Reverier-Xu/KeysDock/arts/nijika.png

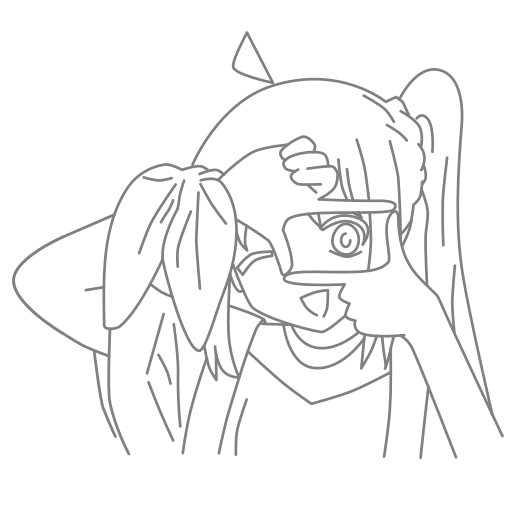
arts/nijika.png
