Reverier-Xu/KeysDock/suitekits/KeysDock.FCStd

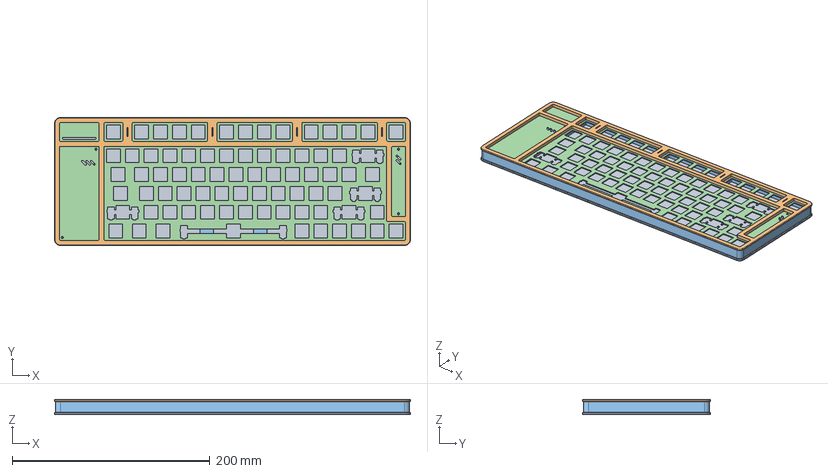
[picture p18: CAD file, 2026-06-06]
suitekits/KeysDock.FCStd
359.8 x 129.3 x 15.0 mm
Base
Cover
Center
Plate
