Reverier-Xu/KeysDock/hardware/models/TPD4E05U06DQAR.step

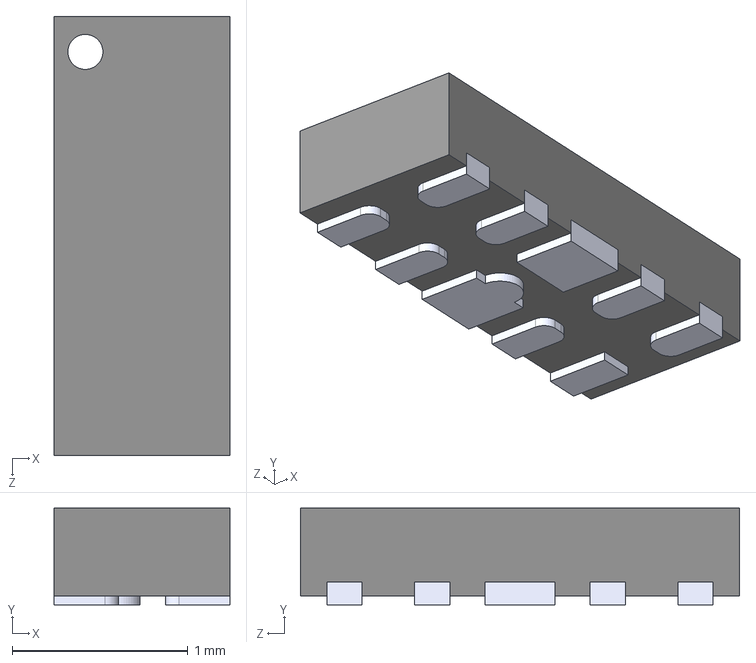
[picture p19: CAD file, 2026-03-23]
hardware/models/TPD4E05U06DQAR.step
1.00 x 0.55 x 2.50 mm
