Reverier-Xu/KeysDock/hardware/models/LED-SMD_XL-3512RGBW.step

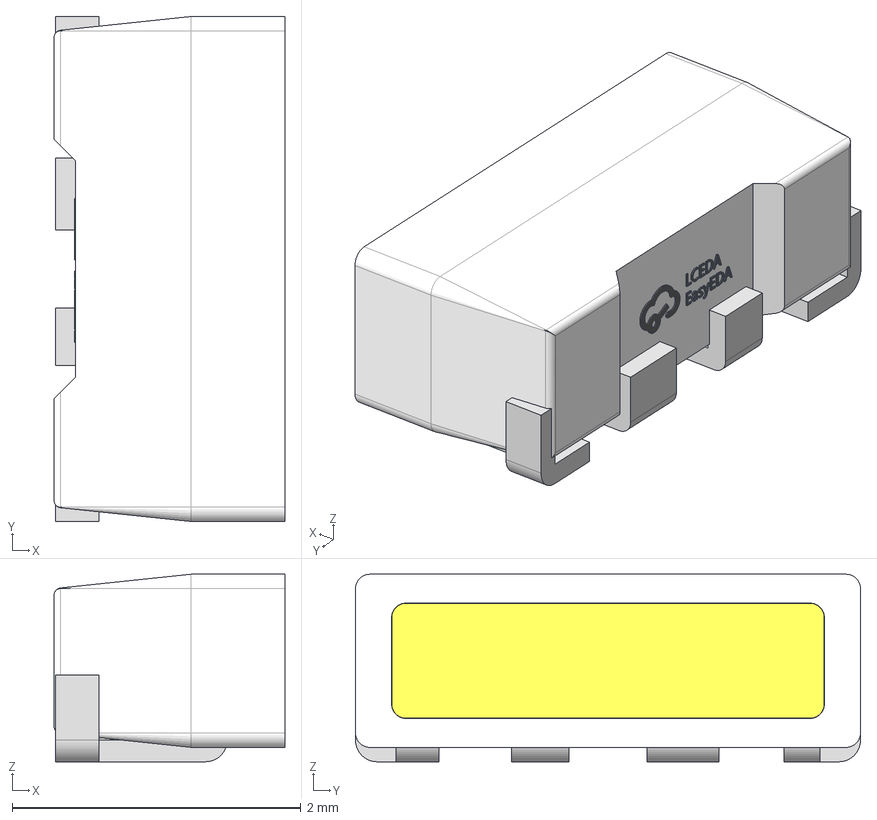
[picture p20: CAD file, 2026-01-06]
hardware/models/LED-SMD_XL-3512RGBW.step
1.60 x 3.50 x 1.30 mm
LED-SMD_XL-3512RGBW~LED-SMD_XL-3512RGBW~Yvv9
LED-SMD_XL-3512RGBW~LED-SMD_XL-3512RGBW~Yvv010
