Reverier-Xu/KeysDock/hardware/models/HC-TYPE-C-16P-CB1.6.step

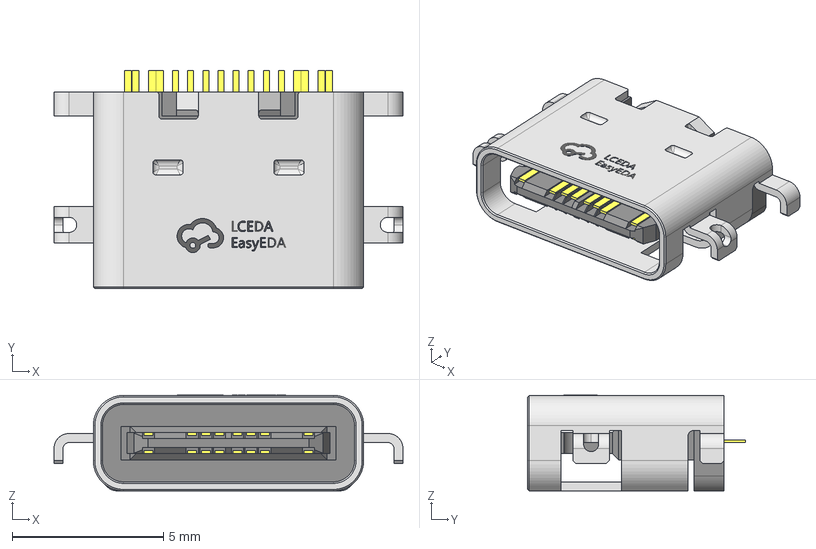
[picture p21: CAD file, 2026-01-03]
hardware/models/HC-TYPE-C-16P-CB1.6.step
11.5 x 7.20 x 3.17 mm
USB-C-SMD_HC-TYPE-C-16P-CB1.6~USB-C-SMD_HC-TYPE-C-16P-CB1.6~1VdE
USB-C-SMD_HC-TYPE-C-16P-CB1.6~USB-C-SMD_HC-TYPE-C-16P-CB1.6~1VdE001
USB-C-SMD_HC-TYPE-C-16P-CB1.6~USB-C-SMD_HC-TYPE-C-16P-CB1.6~1VdE002
USB-C-SMD_HC-TYPE-C-16P-CB1.6~USB-C-SMD_HC-TYPE-C-16P-CB1.6~1VdE003
USB-C-SMD_HC-TYPE-C-16P-CB1.6~USB-C-SMD_HC-TYPE-C-16P-CB1.6~1VdE004
USB-C-SMD_HC-TYPE-C-16P-CB1.6~USB-C-SMD_HC-TYPE-C-16P-CB1.6~1VdE005
USB-C-SMD_HC-TYPE-C-16P-CB1.6~USB-C-SMD_HC-TYPE-C-16P-CB1.6~1VdE006
USB-C-SMD_HC-TYPE-C-16P-CB1.6~USB-C-SMD_HC-TYPE-C-16P-CB1.6~1VdE007
USB-C-SMD_HC-TYPE-C-16P-CB1.6~USB-C-SMD_HC-TYPE-C-16P-CB1.6~1VdE008
USB-C-SMD_HC-TYPE-C-16P-CB1.6~USB-C-SMD_HC-TYPE-C-16P-CB1.6~1VdE009
USB-C-SMD_HC-TYPE-C-16P-CB1.6~USB-C-SMD_HC-TYPE-C-16P-CB1.6~1VdE010
USB-C-SMD_HC-TYPE-C-16P-CB1.6~USB-C-SMD_HC-TYPE-C-16P-CB1.6~1VdE011
USB-C-SMD_HC-TYPE-C-16P-CB1.6~USB-C-SMD_HC-TYPE-C-16P-CB1.6~1VdE012
USB-C-SMD_HC-TYPE-C-16P-CB1.6~USB-C-SMD_HC-TYPE-C-16P-CB1.6~1VdE013
USB-C-SMD_HC-TYPE-C-16P-CB1.6~USB-C-SMD_HC-TYPE-C-16P-CB1.6~1VdE014
USB-C-SMD_HC-TYPE-C-16P-CB1.6~USB-C-SMD_HC-TYPE-C-16P-CB1.6~1VdE015
USB-C-SMD_HC-TYPE-C-16P-CB1.6~USB-C-SMD_HC-TYPE-C-16P-CB1.6~1VdE016
USB-C-SMD_HC-TYPE-C-16P-CB1.6~USB-C-SMD_HC-TYPE-C-16P-CB1.6~1VdE017
USB-C-SMD_HC-TYPE-C-16P-CB1.6~USB-C-SMD_HC-TYPE-C-16P-CB1.6~1VdE018
USB-C-SMD_HC-TYPE-C-16P-CB1.6~USB-C-SMD_HC-TYPE-C-16P-CB1.6~1VdE019
USB-C-SMD_HC-TYPE-C-16P-CB1.6~USB-C-SMD_HC-TYPE-C-16P-CB1.6~1VdE020
USB-C-SMD_HC-TYPE-C-16P-CB1.6~USB-C-SMD_HC-TYPE-C-16P-CB1.6~1VdE021
USB-C-SMD_HC-TYPE-C-16P-CB1.6~USB-C-SMD_HC-TYPE-C-16P-CB1.6~1VdE022
USB-C-SMD_HC-TYPE-C-16P-CB1.6~USB-C-SMD_HC-TYPE-C-16P-CB1.6~1VdE023
USB-C-SMD_HC-TYPE-C-16P-CB1.6~USB-C-SMD_HC-TYPE-C-16P-CB1.6~1VdE024
USB-C-SMD_HC-TYPE-C-16P-CB1.6~USB-C-SMD_HC-TYPE-C-16P-CB1.6~1VdE025
USB-C-SMD_HC-TYPE-C-16P-CB1.6~USB-C-SMD_HC-TYPE-C-16P-CB1.6~1VdE026
USB-C-SMD_HC-TYPE-C-16P-CB1.6~USB-C-SMD_HC-TYPE-C-16P-CB1.6~1VdE027
USB-C-SMD_HC-TYPE-C-16P-CB1.6~USB-C-SMD_HC-TYPE-C-16P-CB1.6~1VdE028
