Reverier-Xu/KeysDock/hardware/models/FPC-SMD_AFA01-S08FCA-00.step

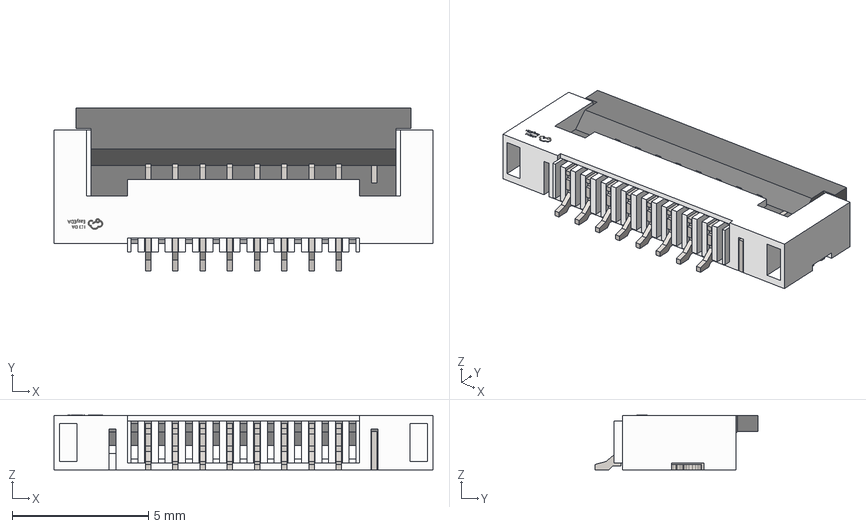
[picture p22: CAD file, 2026-01-03]
hardware/models/FPC-SMD_AFA01-S08FCA-00.step
13.9 x 5.97 x 2.01 mm
FPC-SMD_8P-P1.00_FGS-XJ-H2.0~FPC-SMD_8P-P1.00_FGS-XJ-H2.0~0tRl
FPC-SMD_8P-P1.00_FGS-XJ-H2.0~FPC-SMD_8P-P1.00_FGS-XJ-H2.0~0tRl001
FPC-SMD_8P-P1.00_FGS-XJ-H2.0~FPC-SMD_8P-P1.00_FGS-XJ-H2.0~0tRl002
FPC-SMD_8P-P1.00_FGS-XJ-H2.0~FPC-SMD_8P-P1.00_FGS-XJ-H2.0~0tRl003
FPC-SMD_8P-P1.00_FGS-XJ-H2.0~FPC-SMD_8P-P1.00_FGS-XJ-H2.0~0tRl004
FPC-SMD_8P-P1.00_FGS-XJ-H2.0~FPC-SMD_8P-P1.00_FGS-XJ-H2.0~0tRl005
FPC-SMD_8P-P1.00_FGS-XJ-H2.0~FPC-SMD_8P-P1.00_FGS-XJ-H2.0~0tRl006
FPC-SMD_8P-P1.00_FGS-XJ-H2.0~FPC-SMD_8P-P1.00_FGS-XJ-H2.0~0tRl007
FPC-SMD_8P-P1.00_FGS-XJ-H2.0~FPC-SMD_8P-P1.00_FGS-XJ-H2.0~0tRl008
FPC-SMD_8P-P1.00_FGS-XJ-H2.0~FPC-SMD_8P-P1.00_FGS-XJ-H2.0~0tRl009
FPC-SMD_8P-P1.00_FGS-XJ-H2.0~FPC-SMD_8P-P1.00_FGS-XJ-H2.0~0tRl010
FPC-SMD_8P-P1.00_FGS-XJ-H2.0~FPC-SMD_8P-P1.00_FGS-XJ-H2.0~0tRl011
