Reverier-Xu/KeysDock/hardware/models/EC12E1240301.step

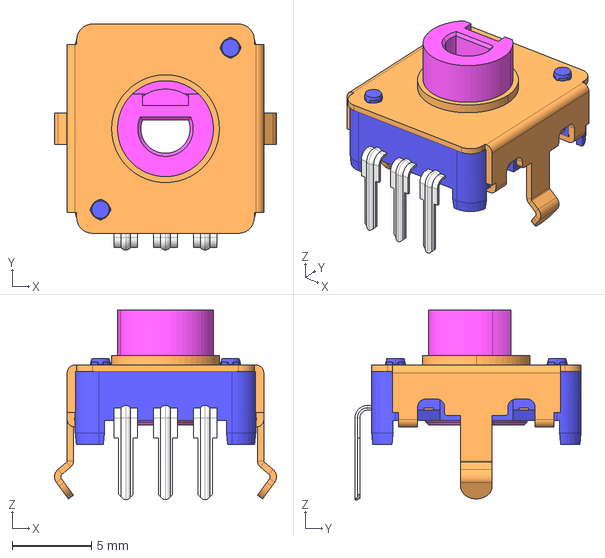
[picture p23: CAD file, 2026-01-02]
hardware/models/EC12E1240301.step
14.0 x 14.3 x 11.9 mm
