Reverier-Xu/KeysDock/hardware/models/HC-1.25-4PWT.step

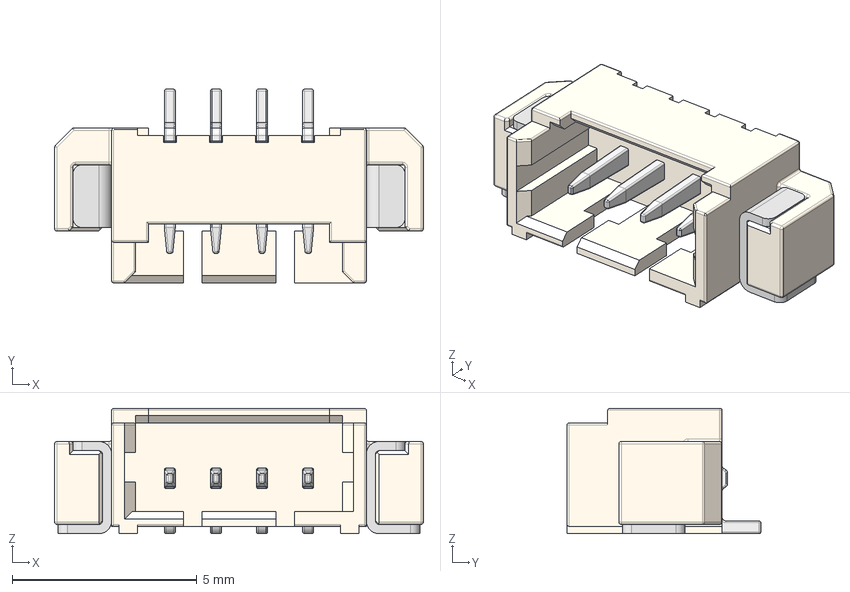
[picture p24: CAD file, 2026-01-02]
hardware/models/HC-1.25-4PWT.step
10.0 x 5.25 x 3.40 mm
CONN-SMD_4P-P1.25-HC-1.25-4PWT~CONN-SMD_4P-P1.25-HC-1.25-4PWT~hYHu002
CONN-SMD_4P-P1.25-HC-1.25-4PWT~CONN-SMD_4P-P1.25-HC-1.25-4PWT~hYHu001
CONN-SMD_4P-P1.25-HC-1.25-4PWT~CONN-SMD_4P-P1.25-HC-1.25-4PWT~hYHu
