Reverier-Xu/KeysDock/hardware/models/TS24CA.step

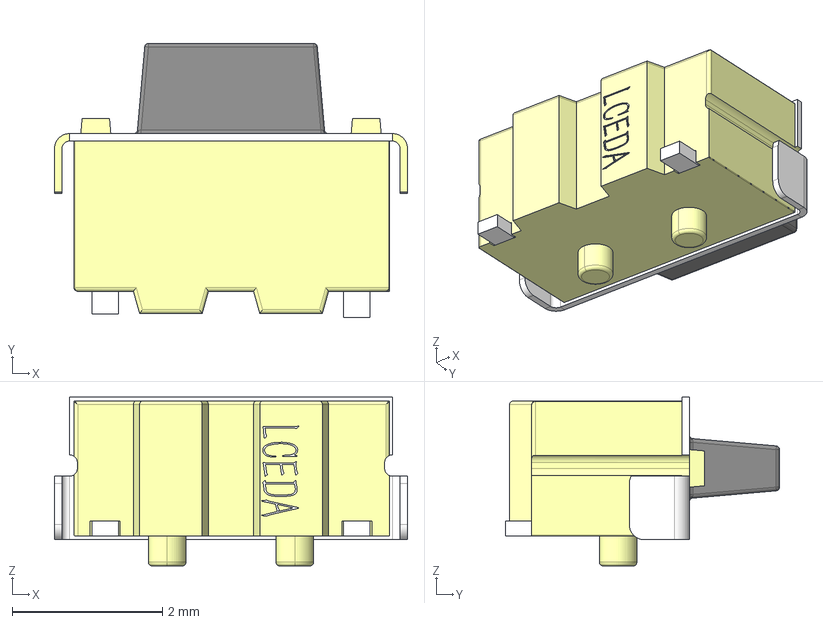
[picture p25: CAD file, 2026-01-02]
hardware/models/TS24CA.step
4.70 x 3.65 x 2.25 mm
SW-SMD_L4.7-W3.5-P3.35-EH~SW-SMD_L4.7-W3.5-H1.9-P3.35-EH~9SV2
SW-SMD_L4.7-W3.5-P3.35-EH~SW-SMD_L4.7-W3.5-H1.9-P3.35-EH~9SV003
SW-SMD_L4.7-W3.5-P3.35-EH~SW-SMD_L4.7-W3.5-H1.9-P3.35-EH~9SV004
