Reverier-Xu/KeysDock/hardware/models/HC-1.25-2PWT.step

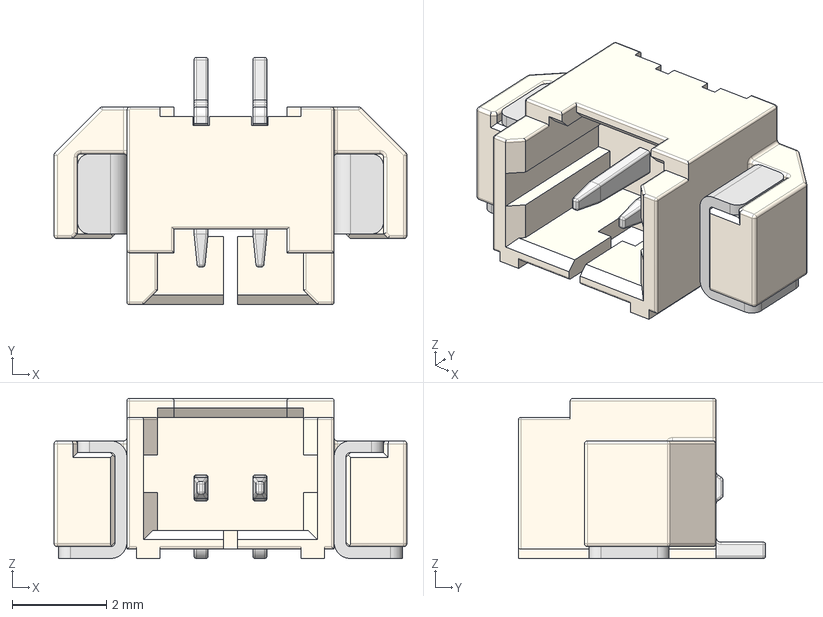
[picture p26: CAD file, 2026-01-02]
hardware/models/HC-1.25-2PWT.step
7.50 x 5.25 x 3.40 mm
CONN-SMD_2P-P1.25-HC-1.25-2PWT~CONN-SMD_2P-P1.25-HC-1.25-2PWT~wzWG
CONN-SMD_2P-P1.25-HC-1.25-2PWT~CONN-SMD_2P-P1.25-HC-1.25-2PWT~wzWG001
CONN-SMD_2P-P1.25-HC-1.25-2PWT~CONN-SMD_2P-P1.25-HC-1.25-2PWT~wzWG002
