Reverier-Xu/KeysDock/hardware/models/BM28-16DS.stp

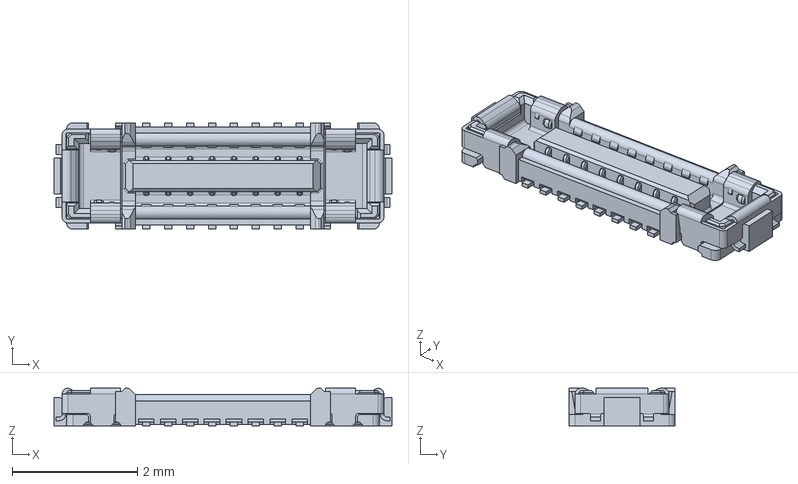
[picture p27: CAD file, 2025-12-31]
hardware/models/BM28-16DS.stp
5.40 x 1.70 x 0.6 mm
