Reverier-Xu/KeysDock/hardware/models/AXK6F16347YG.step

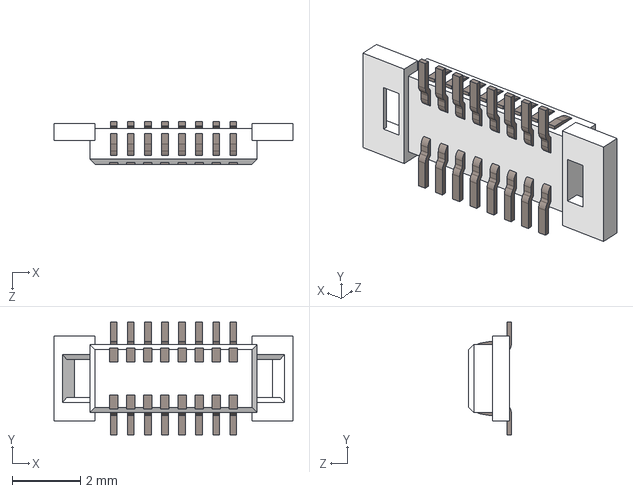
[picture p28: CAD file, 2025-12-31]
hardware/models/AXK6F16347YG.step
7.00 x 3.30 x 1.25 mm
