Reverier-Xu/KeysDock/hardware/models/BM28-16DP.stp

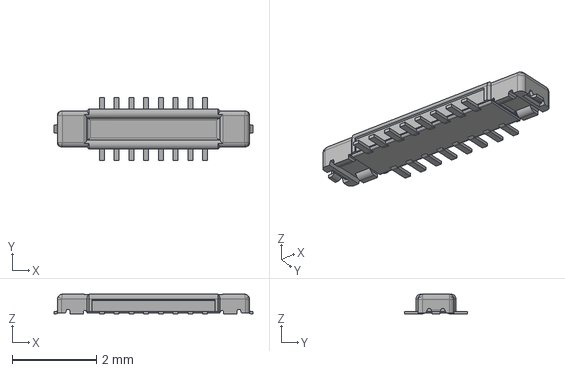
[picture p29: CAD file, 2025-12-31]
hardware/models/BM28-16DP.stp
4.72 x 1.50 x 0.465 mm
