Reverier-Xu/KeysDock/hardware/models/AXK6F20347YG.step

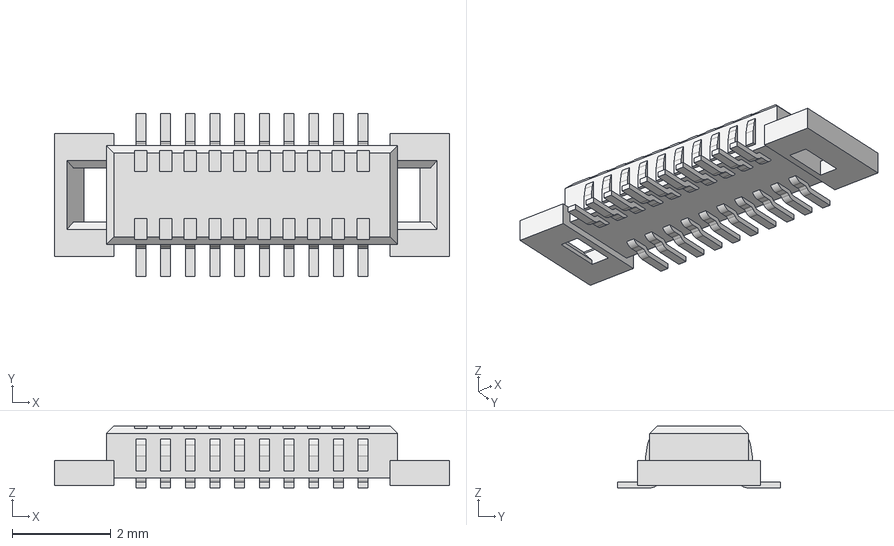
[picture p30: CAD file, 2025-12-31]
hardware/models/AXK6F20347YG.step
8.00 x 3.30 x 1.25 mm
