Reverier-Xu/KeysDock/hardware/models/AXK5F16347YG.step

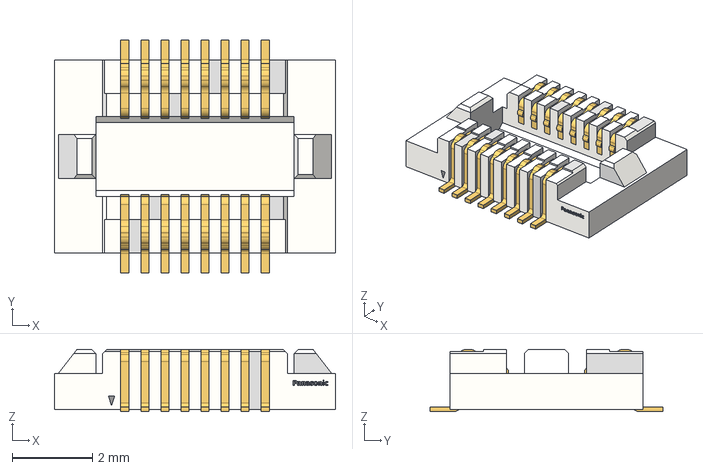
[picture p31: CAD file, 2025-12-31]
hardware/models/AXK5F16347YG.step
7.00 x 5.80 x 1.55 mm
