Reverier-Xu/KeysDock/hardware/models/AXK5F20347YG.step

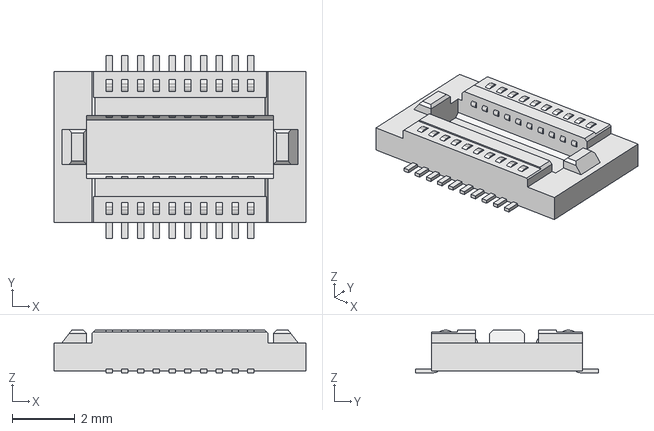
[picture p32: CAD file, 2025-12-31]
hardware/models/AXK5F20347YG.step
8.00 x 5.80 x 1.35 mm
