Reverier-Xu/KeysDock/hardware/models/Crystal_SMD-3225-4P.step

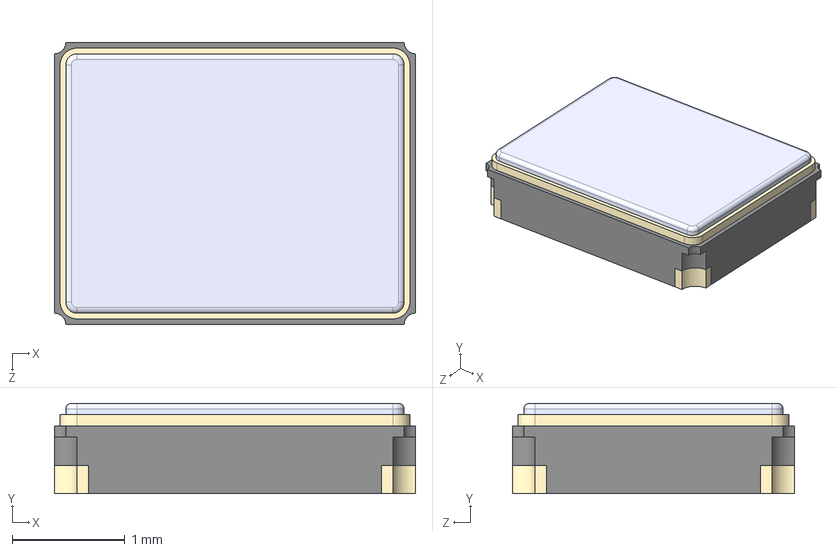
[picture p33: CAD file, 2025-12-29]
hardware/models/Crystal_SMD-3225-4P.step
3.20 x 0.8 x 2.50 mm
