Reverier-Xu/KeysDock/hardware/models/CH343P.step

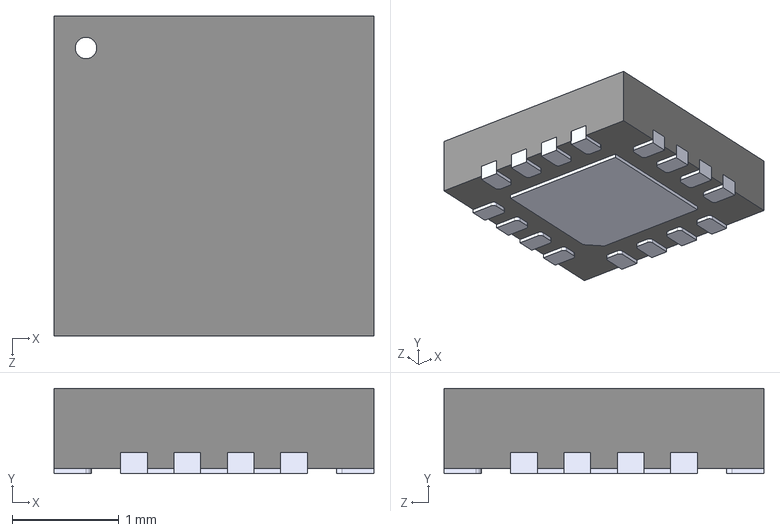
[picture p34: CAD file, 2025-12-19]
hardware/models/CH343P.step
3.00 x 0.8 x 3.00 mm
