Reverier-Xu/KeysDock/hardware/models/SMD_4P-L3.5-W2.8-BR-1.step

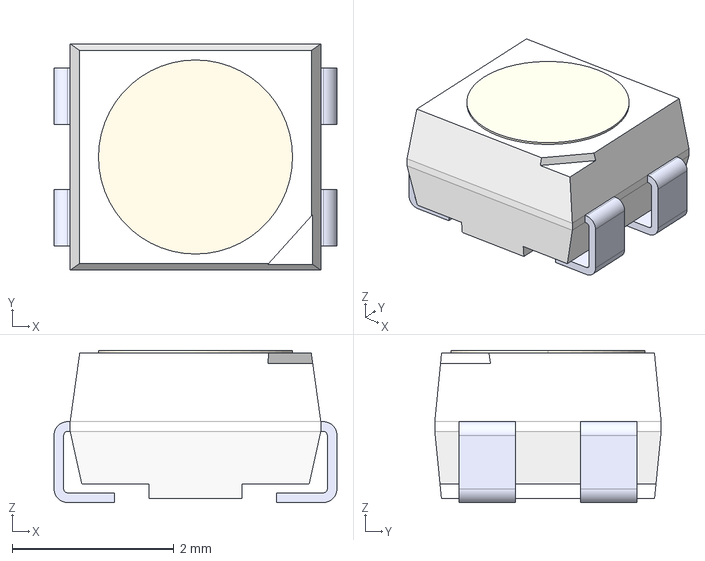
[picture p35: CAD file, 2025-11-28]
hardware/models/SMD_4P-L3.5-W2.8-BR-1.step
3.50 x 2.80 x 1.88 mm
