Reverier-Xu/KeysDock/hardware/models/SW-SMD_SSSS811101.step

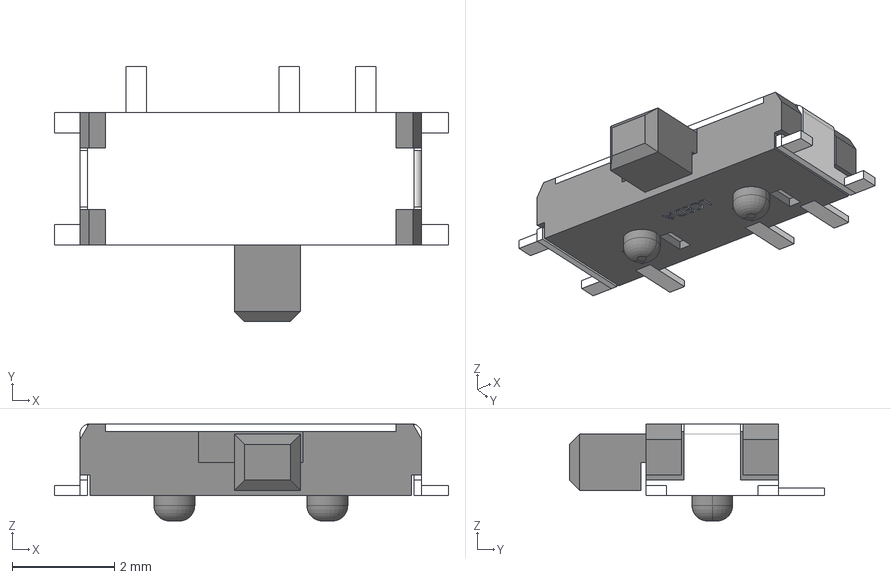
[picture p36: CAD file, 2025-11-28]
hardware/models/SW-SMD_SSSS811101.step
7.72 x 5.00 x 1.90 mm
SW-SMD_SSSS811101~SW-TH_SSSS811101~VVTr
SW-SMD_SSSS811101~SW-TH_SSSS811101~VVTr001
SW-SMD_SSSS811101~SW-TH_SSSS811101~VVTr002
SW-SMD_SSSS811101~SW-TH_SSSS811101~VVTr003
SW-SMD_SSSS811101~SW-TH_SSSS811101~VVTr004
SW-SMD_SSSS811101~SW-TH_SSSS811101~VVTr005
SW-SMD_SSSS811101~SW-TH_SSSS811101~VVTr006
SW-SMD_SSSS811101~SW-TH_SSSS811101~VVTr007
SW-SMD_SSSS811101~SW-TH_SSSS811101~VVTr008
SW-SMD_SSSS811101~SW-TH_SSSS811101~VVTr009
SW-SMD_SSSS811101~SW-TH_SSSS811101~VVTr010
SW-SMD_SSSS811101~SW-TH_SSSS811101~VVTr011
SW-SMD_SSSS811101~SW-TH_SSSS811101~VVTr012
SW-SMD_SSSS811101~SW-TH_SSSS811101~VVTr013
SW-SMD_SSSS811101~SW-TH_SSSS811101~VVTr014
SW-SMD_SSSS811101~SW-TH_SSSS811101~VVTr015
SW-SMD_SSSS811101~SW-TH_SSSS811101~VVTr016
SW-SMD_SSSS811101~SW-TH_SSSS811101~VVTr017
