Reverier-Xu/KeysDock/hardware/models/D_SOD-123FL.step

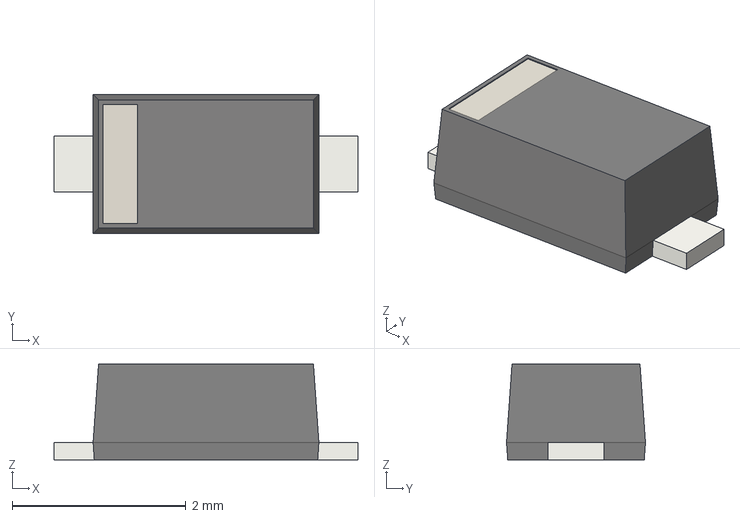
[picture p37: CAD file, 2025-11-16]
hardware/models/D_SOD-123FL.step
3.50 x 1.60 x 1.10 mm
