Reverier-Xu/KeysDock/hardware/models/TSSOP-24_L7.8-W4.4-H1.0-LS6.4-P0.65.step

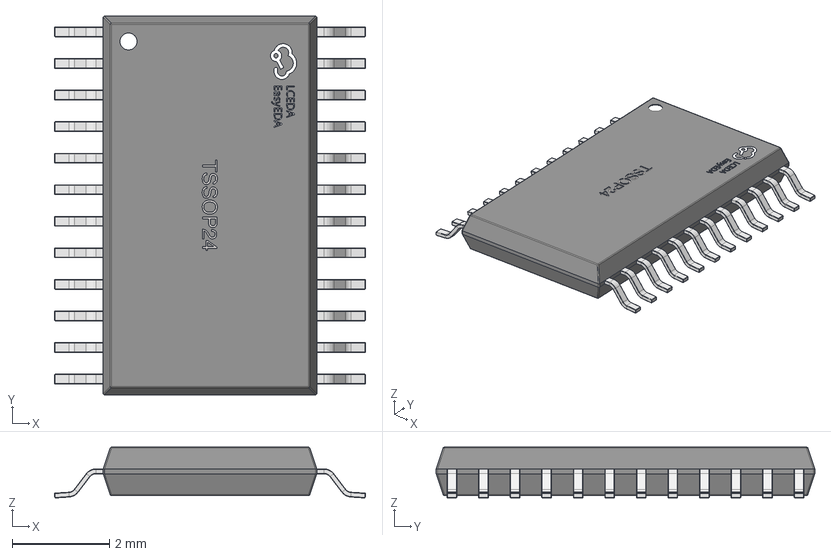
[picture p38: CAD file, 2025-11-09]
hardware/models/TSSOP-24_L7.8-W4.4-H1.0-LS6.4-P0.65.step
6.41 x 7.80 x 1.05 mm
TSSOP-24_L7.8-W4.4-P0.65-LS6.4-BL~TSSOP-24_ L7.8-W4.4-H1.0-LS6.4-P0.65~5FKe
TSSOP-24_L7.8-W4.4-P0.65-LS6.4-BL~TSSOP-24_ L7.8-W4.4-H1.0-LS6.4-P0.65~5FKe001
TSSOP-24_L7.8-W4.4-P0.65-LS6.4-BL~TSSOP-24_ L7.8-W4.4-H1.0-LS6.4-P0.65~5FKe002
TSSOP-24_L7.8-W4.4-P0.65-LS6.4-BL~TSSOP-24_ L7.8-W4.4-H1.0-LS6.4-P0.65~5FKe003
TSSOP-24_L7.8-W4.4-P0.65-LS6.4-BL~TSSOP-24_ L7.8-W4.4-H1.0-LS6.4-P0.65~5FKe004
TSSOP-24_L7.8-W4.4-P0.65-LS6.4-BL~TSSOP-24_ L7.8-W4.4-H1.0-LS6.4-P0.65~5FKe005
TSSOP-24_L7.8-W4.4-P0.65-LS6.4-BL~TSSOP-24_ L7.8-W4.4-H1.0-LS6.4-P0.65~5FKe006
TSSOP-24_L7.8-W4.4-P0.65-LS6.4-BL~TSSOP-24_ L7.8-W4.4-H1.0-LS6.4-P0.65~5FKe007
TSSOP-24_L7.8-W4.4-P0.65-LS6.4-BL~TSSOP-24_ L7.8-W4.4-H1.0-LS6.4-P0.65~5FKe008
TSSOP-24_L7.8-W4.4-P0.65-LS6.4-BL~TSSOP-24_ L7.8-W4.4-H1.0-LS6.4-P0.65~5FKe009
TSSOP-24_L7.8-W4.4-P0.65-LS6.4-BL~TSSOP-24_ L7.8-W4.4-H1.0-LS6.4-P0.65~5FKe010
TSSOP-24_L7.8-W4.4-P0.65-LS6.4-BL~TSSOP-24_ L7.8-W4.4-H1.0-LS6.4-P0.65~5FKe011
TSSOP-24_L7.8-W4.4-P0.65-LS6.4-BL~TSSOP-24_ L7.8-W4.4-H1.0-LS6.4-P0.65~5FKe012
TSSOP-24_L7.8-W4.4-P0.65-LS6.4-BL~TSSOP-24_ L7.8-W4.4-H1.0-LS6.4-P0.65~5FKe013
TSSOP-24_L7.8-W4.4-P0.65-LS6.4-BL~TSSOP-24_ L7.8-W4.4-H1.0-LS6.4-P0.65~5FKe014
TSSOP-24_L7.8-W4.4-P0.65-LS6.4-BL~TSSOP-24_ L7.8-W4.4-H1.0-LS6.4-P0.65~5FKe015
TSSOP-24_L7.8-W4.4-P0.65-LS6.4-BL~TSSOP-24_ L7.8-W4.4-H1.0-LS6.4-P0.65~5FKe016
TSSOP-24_L7.8-W4.4-P0.65-LS6.4-BL~TSSOP-24_ L7.8-W4.4-H1.0-LS6.4-P0.65~5FKe017
TSSOP-24_L7.8-W4.4-P0.65-LS6.4-BL~TSSOP-24_ L7.8-W4.4-H1.0-LS6.4-P0.65~5FKe018
TSSOP-24_L7.8-W4.4-P0.65-LS6.4-BL~TSSOP-24_ L7.8-W4.4-H1.0-LS6.4-P0.65~5FKe019
TSSOP-24_L7.8-W4.4-P0.65-LS6.4-BL~TSSOP-24_ L7.8-W4.4-H1.0-LS6.4-P0.65~5FKe020
TSSOP-24_L7.8-W4.4-P0.65-LS6.4-BL~TSSOP-24_ L7.8-W4.4-H1.0-LS6.4-P0.65~5FKe021
TSSOP-24_L7.8-W4.4-P0.65-LS6.4-BL~TSSOP-24_ L7.8-W4.4-H1.0-LS6.4-P0.65~5FKe022
TSSOP-24_L7.8-W4.4-P0.65-LS6.4-BL~TSSOP-24_ L7.8-W4.4-H1.0-LS6.4-P0.65~5FKe023
TSSOP-24_L7.8-W4.4-P0.65-LS6.4-BL~TSSOP-24_ L7.8-W4.4-H1.0-LS6.4-P0.65~5FKe024
TSSOP-24_L7.8-W4.4-P0.65-LS6.4-BL~TSSOP-24_ L7.8-W4.4-H1.0-LS6.4-P0.65~5FKe025
TSSOP-24_L7.8-W4.4-P0.65-LS6.4-BL~TSSOP-24_ L7.8-W4.4-H1.0-LS6.4-P0.65~5FKe026
TSSOP-24_L7.8-W4.4-P0.65-LS6.4-BL~TSSOP-24_ L7.8-W4.4-H1.0-LS6.4-P0.65~5FKe027
TSSOP-24_L7.8-W4.4-P0.65-LS6.4-BL~TSSOP-24_ L7.8-W4.4-H1.0-LS6.4-P0.65~5FKe028
TSSOP-24_L7.8-W4.4-P0.65-LS6.4-BL~TSSOP-24_ L7.8-W4.4-H1.0-LS6.4-P0.65~5FKe029
TSSOP-24_L7.8-W4.4-P0.65-LS6.4-BL~TSSOP-24_ L7.8-W4.4-H1.0-LS6.4-P0.65~5FKe030
TSSOP-24_L7.8-W4.4-P0.65-LS6.4-BL~TSSOP-24_ L7.8-W4.4-H1.0-LS6.4-P0.65~5FKe031
TSSOP-24_L7.8-W4.4-P0.65-LS6.4-BL~TSSOP-24_ L7.8-W4.4-H1.0-LS6.4-P0.65~5FKe032
TSSOP-24_L7.8-W4.4-P0.65-LS6.4-BL~TSSOP-24_ L7.8-W4.4-H1.0-LS6.4-P0.65~5FKe033
TSSOP-24_L7.8-W4.4-P0.65-LS6.4-BL~TSSOP-24_ L7.8-W4.4-H1.0-LS6.4-P0.65~5FKe034
TSSOP-24_L7.8-W4.4-P0.65-LS6.4-BL~TSSOP-24_ L7.8-W4.4-H1.0-LS6.4-P0.65~5FKe035
TSSOP-24_L7.8-W4.4-P0.65-LS6.4-BL~TSSOP-24_ L7.8-W4.4-H1.0-LS6.4-P0.65~5FKe036
TSSOP-24_L7.8-W4.4-P0.65-LS6.4-BL~TSSOP-24_ L7.8-W4.4-H1.0-LS6.4-P0.65~5FKe037
