Reverier-Xu/KeysDock/hardware/models/IND-SMD_L2.5-W2.0_MHCHL2520.step

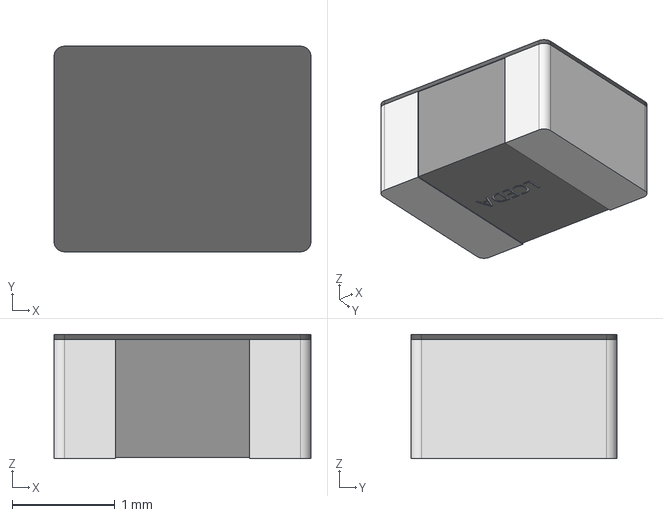
[picture p39: CAD file, 2025-11-08]
hardware/models/IND-SMD_L2.5-W2.0_MHCHL2520.step
2.50 x 2.00 x 1.21 mm
IND-SMD_L2.5-W2.0_MHCHL2520~IND-SMD_L2.5-W2.0_MHCHL2520~6FDJ
IND-SMD_L2.5-W2.0_MHCHL2520~IND-SMD_L2.5-W2.0_MHCHL2520~6FDJ001
