Reverier-Xu/KeysDock/hardware/models/L_0805.step

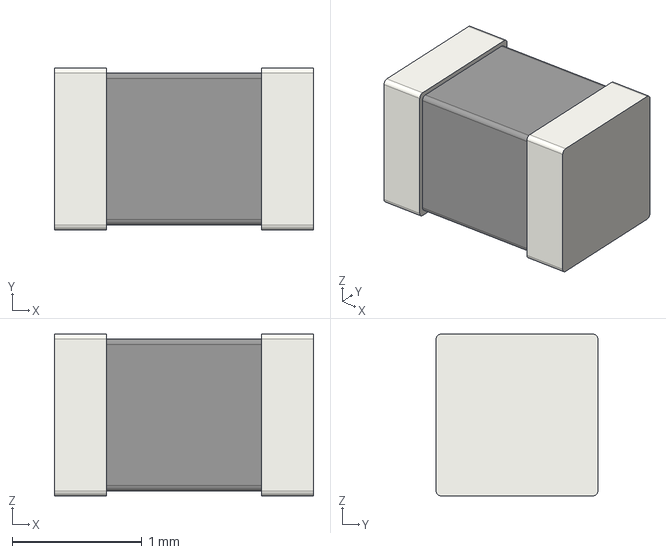
[picture p40: CAD file, 2025-11-08]
hardware/models/L_0805.step
2.00 x 1.25 x 1.25 mm
