Reverier-Xu/KeysDock/hardware/models/TS-1088-AR02016.step

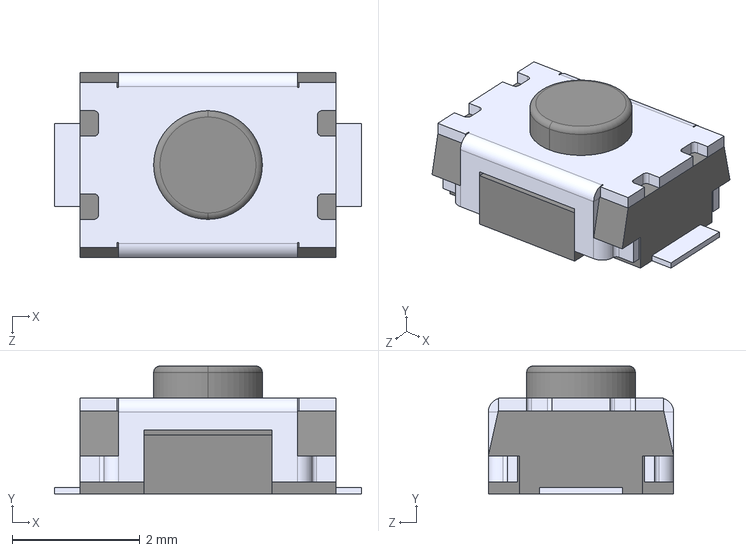
[picture p41: CAD file, 2025-11-08]
hardware/models/TS-1088-AR02016.step
4.80 x 2.00 x 2.90 mm
