Reverier-Xu/KeysDock/hardware/models/SOT-223-4P_L6.5-W3.5-H1.6-LS7.0-P2.30.step

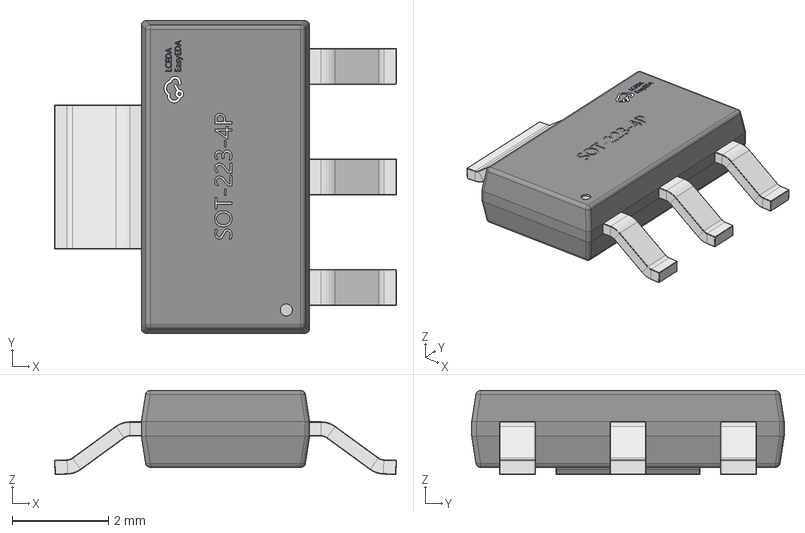
[picture p42: CAD file, 2025-11-04]
hardware/models/SOT-223-4P_L6.5-W3.5-H1.6-LS7.0-P2.30.step
7.11 x 6.50 x 1.75 mm
SOT-223_L6.7-W3.5-P2.30-BR~SOT-223-4P_L6.5-W3.5-H1.6-LS7.0-P2.30~N3MX
SOT-223_L6.7-W3.5-P2.30-BR~SOT-223-4P_ L6.5-W3.5-H1.6-LS7.0-P2.30~N3MX001
SOT-223_L6.7-W3.5-P2.30-BR~SOT-223-4P_ L6.5-W3.5-H1.6-LS7.0-P2.30~N3MX002
SOT-223_L6.7-W3.5-P2.30-BR~SOT-223-4P_ L6.5-W3.5-H1.6-LS7.0-P2.30~N3MX003
SOT-223_L6.7-W3.5-P2.30-BR~SOT-223-4P_ L6.5-W3.5-H1.6-LS7.0-P2.30~N3MX004
SOT-223_L6.7-W3.5-P2.30-BR~SOT-223-4P_ L6.5-W3.5-H1.6-LS7.0-P2.30~N3MX005
SOT-223_L6.7-W3.5-P2.30-BR~SOT-223-4P_ L6.5-W3.5-H1.6-LS7.0-P2.30~N3MX006
SOT-223_L6.7-W3.5-P2.30-BR~SOT-223-4P_ L6.5-W3.5-H1.6-LS7.0-P2.30~N3MX007
SOT-223_L6.7-W3.5-P2.30-BR~SOT-223-4P_ L6.5-W3.5-H1.6-LS7.0-P2.30~N3MX008
SOT-223_L6.7-W3.5-P2.30-BR~SOT-223-4P_ L6.5-W3.5-H1.6-LS7.0-P2.30~N3MX009
SOT-223_L6.7-W3.5-P2.30-BR~SOT-223-4P_ L6.5-W3.5-H1.6-LS7.0-P2.30~N3MX010
SOT-223_L6.7-W3.5-P2.30-BR~SOT-223-4P_ L6.5-W3.5-H1.6-LS7.0-P2.30~N3MX011
SOT-223_L6.7-W3.5-P2.30-BR~SOT-223-4P_ L6.5-W3.5-H1.6-LS7.0-P2.30~N3MX012
SOT-223_L6.7-W3.5-P2.30-BR~SOT-223-4P_ L6.5-W3.5-H1.6-LS7.0-P2.30~N3MX013
SOT-223_L6.7-W3.5-P2.30-BR~SOT-223-4P_ L6.5-W3.5-H1.6-LS7.0-P2.30~N3MX014
SOT-223_L6.7-W3.5-P2.30-BR~SOT-223-4P_ L6.5-W3.5-H1.6-LS7.0-P2.30~N3MX015
SOT-223_L6.7-W3.5-P2.30-BR~SOT-223-4P_ L6.5-W3.5-H1.6-LS7.0-P2.30~N3MX016
SOT-223_L6.7-W3.5-P2.30-BR~SOT-223-4P_ L6.5-W3.5-H1.6-LS7.0-P2.30~N3MX017
