Reverier-Xu/KeysDock/hardware/models/ZX-ZH1.5-3PWT.step

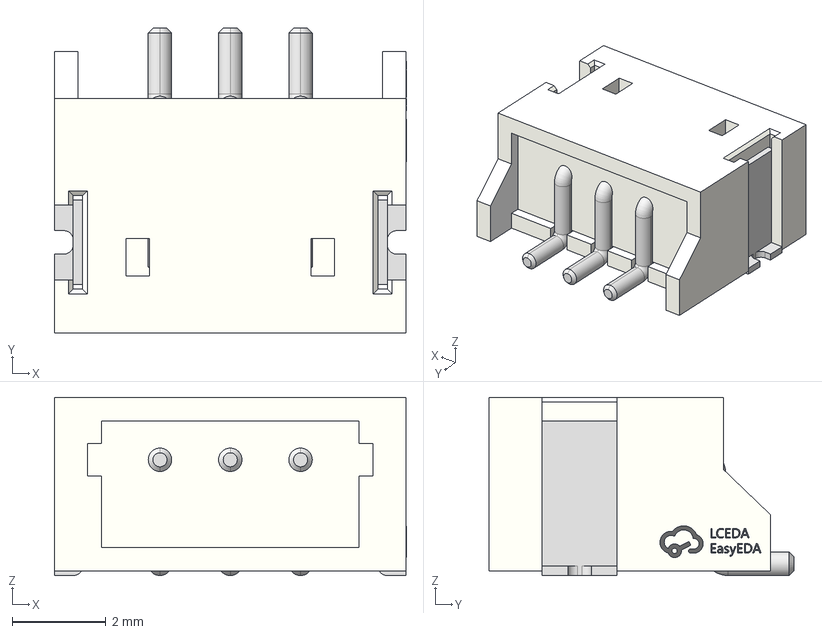
[picture p43: CAD file, 2025-11-03]
hardware/models/ZX-ZH1.5-3PWT.step
7.51 x 6.50 x 3.80 mm
CONN-SMD_3P-P1.50_ZX-ZH1.5-3PWT~CONN-SMD_3P-P1.50_ZX-ZH1.5-3PWT~Tjfn
CONN-SMD_3P-P1.50_ZX-ZH1.5-3PWT~CONN-SMD_3P-P1.50_ ZX-ZH1.5-3PWT~Tjfn001
CONN-SMD_3P-P1.50_ZX-ZH1.5-3PWT~CONN-SMD_3P-P1.50_ ZX-ZH1.5-3PWT~Tjfn002
