Reverier-Xu/KeysDock/hardware/models/ZX-ZH1.5-2PWT.step

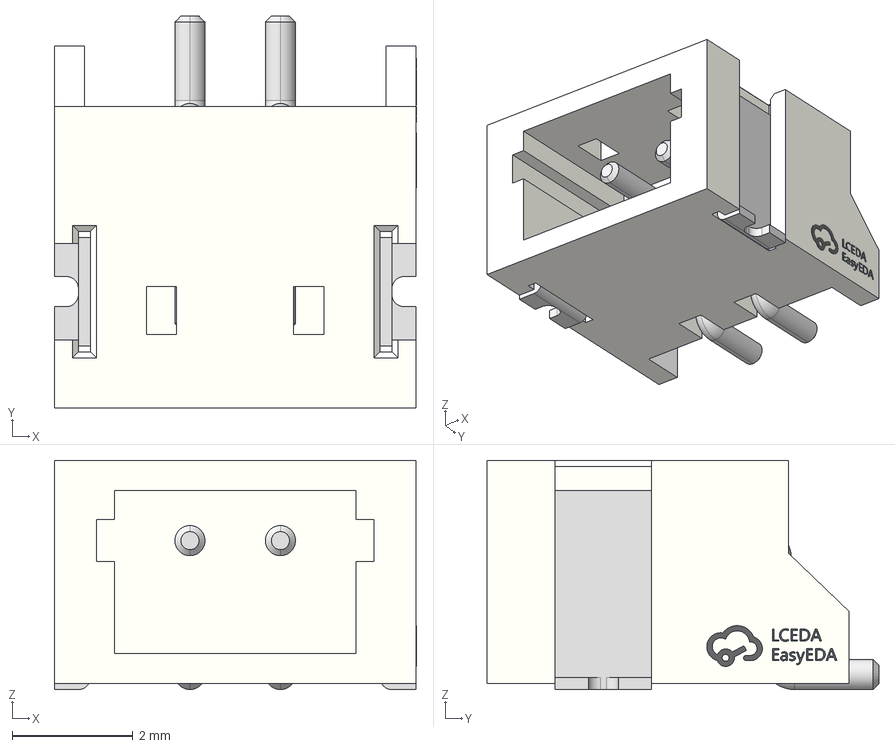
[picture p44: CAD file, 2025-11-03]
hardware/models/ZX-ZH1.5-2PWT.step
6.01 x 6.50 x 3.80 mm
CONN-SMD_2P-P1.50_ZX-ZH1.5-2PWT~CONN-SMD_2P-P1.50_ZX-ZH1.5-2PWT~Tjfn
CONN-SMD_2P-P1.50_ZX-ZH1.5-2PWT~CONN-SMD_2P-P1.50_ ZX-ZH1.5-2PWT~Tjfn001
CONN-SMD_2P-P1.50_ZX-ZH1.5-2PWT~CONN-SMD_2P-P1.50_ ZX-ZH1.5-2PWT~Tjfn002
