Reverier-Xu/KeysDock/hardware/models/TYPE-C-SMD_HX-TYPE-C-16PIN.step

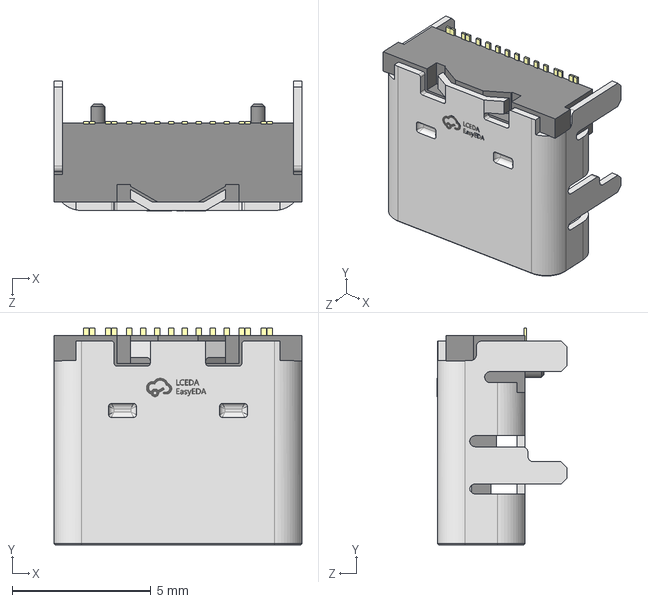
[picture p45: CAD file, 2025-11-03]
hardware/models/TYPE-C-SMD_HX-TYPE-C-16PIN.step
8.94 x 7.82 x 4.67 mm
