Reverier-Xu/KeysDock/hardware/models/FPC-SMD_P0.50-16P_FGS-XJ-H2.0.step

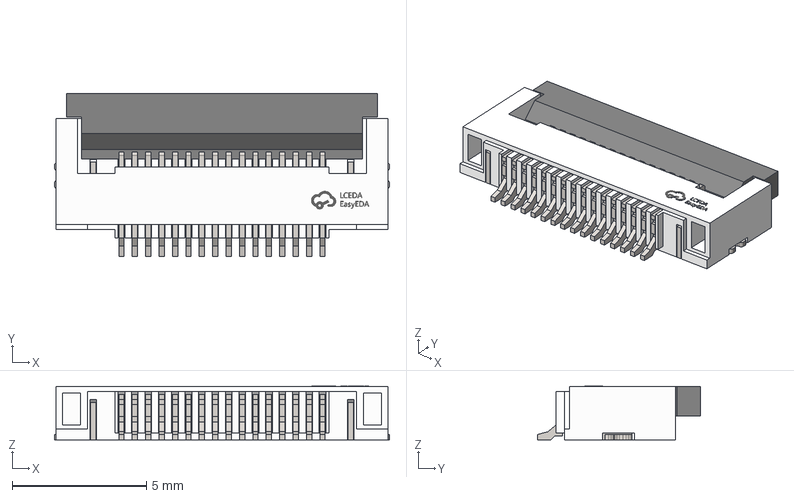
[picture p46: CAD file, 2025-11-01]
hardware/models/FPC-SMD_P0.50-16P_FGS-XJ-H2.0.step
12.5 x 6.10 x 2.01 mm
FPC-SMD_P0.50-16P_FGS-XJ-H2.0~FPC-SMD_P0.50-16P_FGS-XJ-H2.0~IVTd
FPC-SMD_P0.50-16P_FGS-XJ-H2.0~FPC-SMD_P0.50-16P_FGS-XJ-H2.0~IVTd001
FPC-SMD_P0.50-16P_FGS-XJ-H2.0~FPC-SMD_P0.50-16P_FGS-XJ-H2.0~IVTd002
FPC-SMD_P0.50-16P_FGS-XJ-H2.0~FPC-SMD_P0.50-16P_FGS-XJ-H2.0~IVTd003
FPC-SMD_P0.50-16P_FGS-XJ-H2.0~FPC-SMD_P0.50-16P_FGS-XJ-H2.0~IVTd004
FPC-SMD_P0.50-16P_FGS-XJ-H2.0~FPC-SMD_P0.50-16P_FGS-XJ-H2.0~IVTd005
FPC-SMD_P0.50-16P_FGS-XJ-H2.0~FPC-SMD_P0.50-16P_FGS-XJ-H2.0~IVTd006
FPC-SMD_P0.50-16P_FGS-XJ-H2.0~FPC-SMD_P0.50-16P_FGS-XJ-H2.0~IVTd007
FPC-SMD_P0.50-16P_FGS-XJ-H2.0~FPC-SMD_P0.50-16P_FGS-XJ-H2.0~IVTd008
FPC-SMD_P0.50-16P_FGS-XJ-H2.0~FPC-SMD_P0.50-16P_FGS-XJ-H2.0~IVTd009
FPC-SMD_P0.50-16P_FGS-XJ-H2.0~FPC-SMD_P0.50-16P_FGS-XJ-H2.0~IVTd010
FPC-SMD_P0.50-16P_FGS-XJ-H2.0~FPC-SMD_P0.50-16P_FGS-XJ-H2.0~IVTd011
FPC-SMD_P0.50-16P_FGS-XJ-H2.0~FPC-SMD_P0.50-16P_FGS-XJ-H2.0~IVTd012
FPC-SMD_P0.50-16P_FGS-XJ-H2.0~FPC-SMD_P0.50-16P_FGS-XJ-H2.0~IVTd013
FPC-SMD_P0.50-16P_FGS-XJ-H2.0~FPC-SMD_P0.50-16P_FGS-XJ-H2.0~IVTd014
FPC-SMD_P0.50-16P_FGS-XJ-H2.0~FPC-SMD_P0.50-16P_FGS-XJ-H2.0~IVTd015
FPC-SMD_P0.50-16P_FGS-XJ-H2.0~FPC-SMD_P0.50-16P_FGS-XJ-H2.0~IVTd016
FPC-SMD_P0.50-16P_FGS-XJ-H2.0~FPC-SMD_P0.50-16P_FGS-XJ-H2.0~IVTd017
FPC-SMD_P0.50-16P_FGS-XJ-H2.0~FPC-SMD_P0.50-16P_FGS-XJ-H2.0~IVTd018
FPC-SMD_P0.50-16P_FGS-XJ-H2.0~FPC-SMD_P0.50-16P_FGS-XJ-H2.0~IVTd019
