Reverier-Xu/KeysDock/hardware/models/FPC-SMD_AFC01-S12FCA-00.step

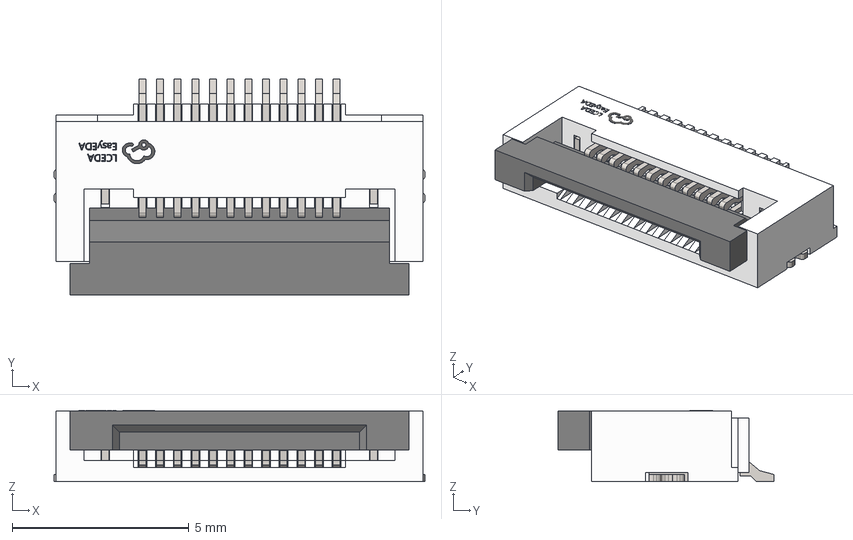
[picture p47: CAD file, 2025-10-30]
hardware/models/FPC-SMD_AFC01-S12FCA-00.step
10.5 x 6.10 x 2.01 mm
FPC-SMD_AFC01-S12FCA-00~FPC-SMD_AFC01-S12FCA-00~WwAV
FPC-SMD_AFC01-S12FCA-00~FPC-SMD_AFC01-S12FCA-00~WwAV001
FPC-SMD_AFC01-S12FCA-00~FPC-SMD_AFC01-S12FCA-00~WwAV002
FPC-SMD_AFC01-S12FCA-00~FPC-SMD_AFC01-S12FCA-00~WwAV003
FPC-SMD_AFC01-S12FCA-00~FPC-SMD_AFC01-S12FCA-00~WwAV004
FPC-SMD_AFC01-S12FCA-00~FPC-SMD_AFC01-S12FCA-00~WwAV005
FPC-SMD_AFC01-S12FCA-00~FPC-SMD_AFC01-S12FCA-00~WwAV006
FPC-SMD_AFC01-S12FCA-00~FPC-SMD_AFC01-S12FCA-00~WwAV007
FPC-SMD_AFC01-S12FCA-00~FPC-SMD_AFC01-S12FCA-00~WwAV008
FPC-SMD_AFC01-S12FCA-00~FPC-SMD_AFC01-S12FCA-00~WwAV009
FPC-SMD_AFC01-S12FCA-00~FPC-SMD_AFC01-S12FCA-00~WwAV010
FPC-SMD_AFC01-S12FCA-00~FPC-SMD_AFC01-S12FCA-00~WwAV011
FPC-SMD_AFC01-S12FCA-00~FPC-SMD_AFC01-S12FCA-00~WwAV012
FPC-SMD_AFC01-S12FCA-00~FPC-SMD_AFC01-S12FCA-00~WwAV013
FPC-SMD_AFC01-S12FCA-00~FPC-SMD_AFC01-S12FCA-00~WwAV014
FPC-SMD_AFC01-S12FCA-00~FPC-SMD_AFC01-S12FCA-00~WwAV015
