Reverier-Xu/KeysDock/hardware/models/SOP-24_L15.2-W7.8-H2.6-LS10.6-P1.27.step

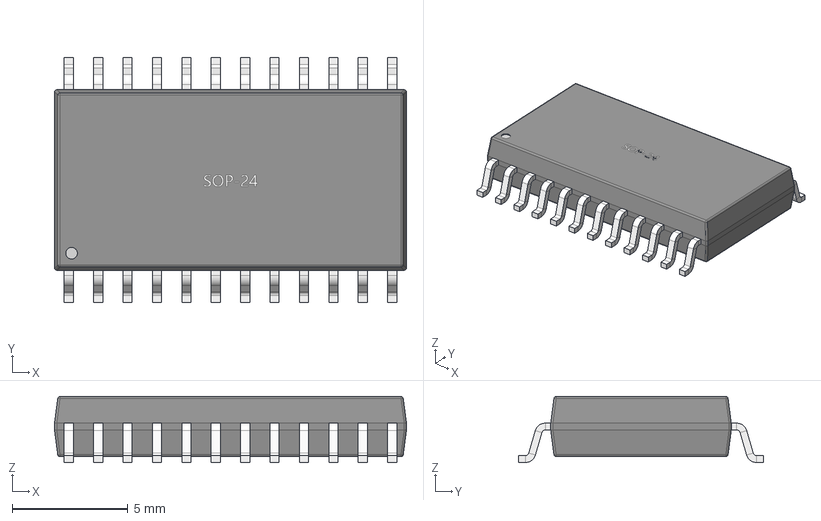
[picture p48: CAD file, 2025-10-28]
hardware/models/SOP-24_L15.2-W7.8-H2.6-LS10.6-P1.27.step
15.2 x 10.6 x 2.85 mm
