Reverier-Xu/KeysDock/hardware/models/SOT-23-6_L2.9-W1.6-P0.95-LS2.8-BR.step

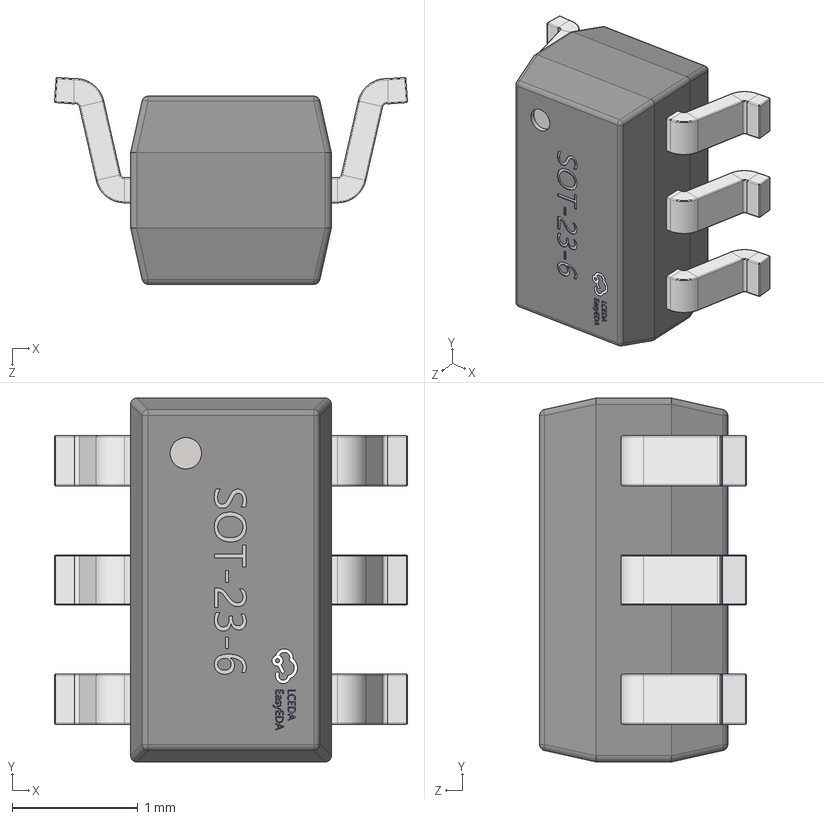
[picture p49: CAD file, 2025-10-28]
hardware/models/SOT-23-6_L2.9-W1.6-P0.95-LS2.8-BR.step
2.81 x 2.90 x 1.65 mm
