Reverier-Xu/KeysDock/hardware/models/C_0603.step

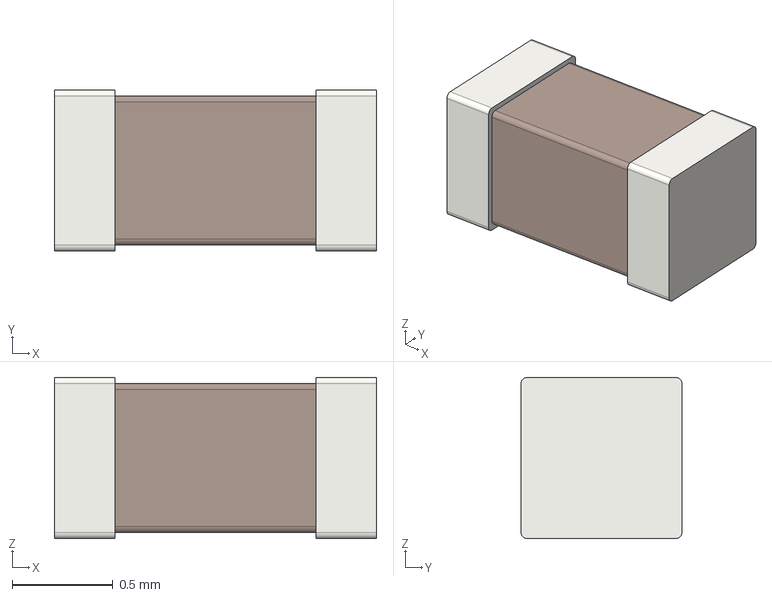
[picture p50: CAD file, 2025-10-28]
hardware/models/C_0603.step
1.60 x 0.8 x 0.8 mm
