Reverier-Xu/KeysDock/hardware/models/R_0402.step

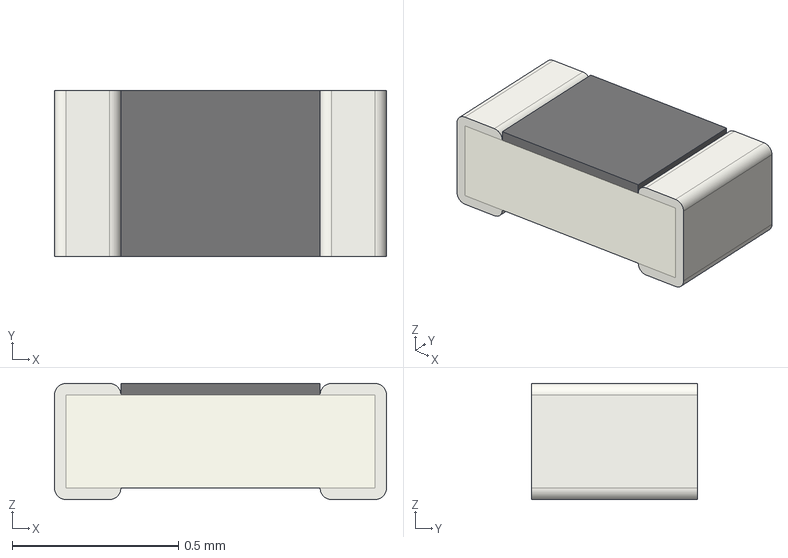
[picture p51: CAD file, 2025-10-28]
hardware/models/R_0402.step
1.00 x 0.5 x 0.35 mm
