Reverier-Xu/KeysDock/hardware/models/LED-SMD_4P_XL-6028RGBW-WS2812B.step

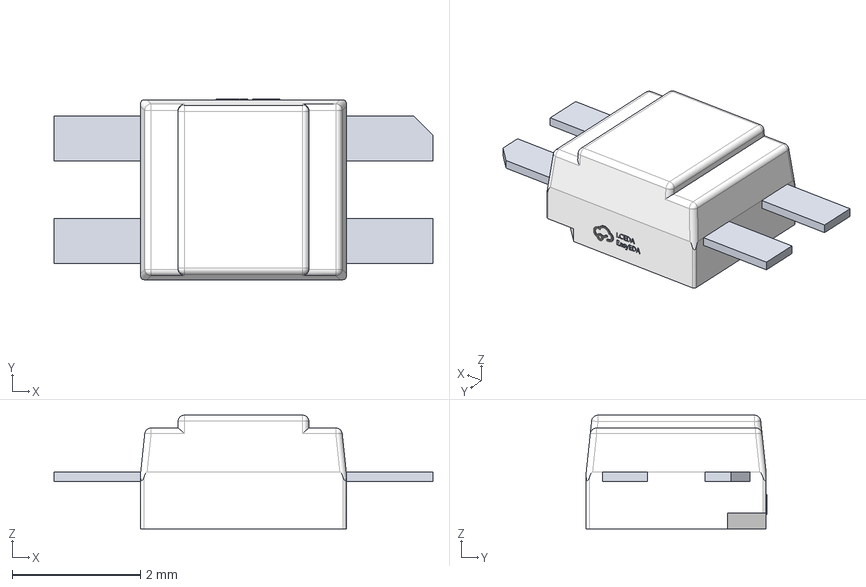
[picture p52: CAD file, 2025-10-28]
hardware/models/LED-SMD_4P_XL-6028RGBW-WS2812B.step
5.90 x 2.81 x 1.77 mm
LED-SMD_4P_XL-6028RGBW-WS2812B~LED-SMD_4P_XL-6028RGBW-WS2812B~1bUX
LED-SMD_4P_XL-6028RGBW-WS2812B~LED-SMD_4P_XL-6028RGBW-WS2812B~1bUX001
