Reverier-Xu/KeysDock/hardware/models/C_0402.step

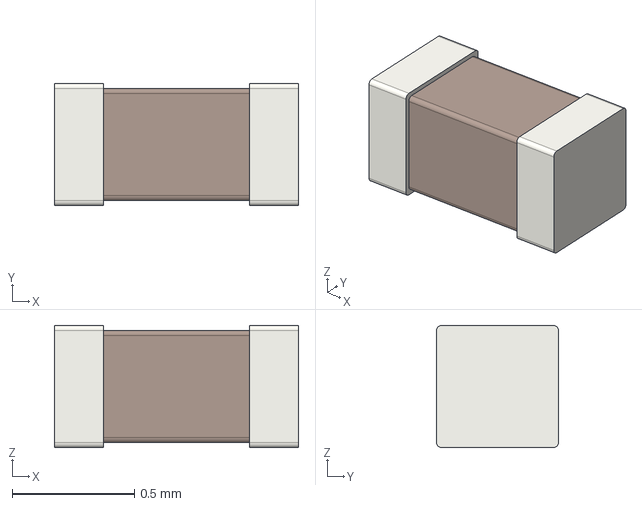
[picture p53: CAD file, 2025-10-28]
hardware/models/C_0402.step
1.00 x 0.5 x 0.5 mm
