Reverier-Xu/KeysDock/hardware/models/KS-33D-FB.step

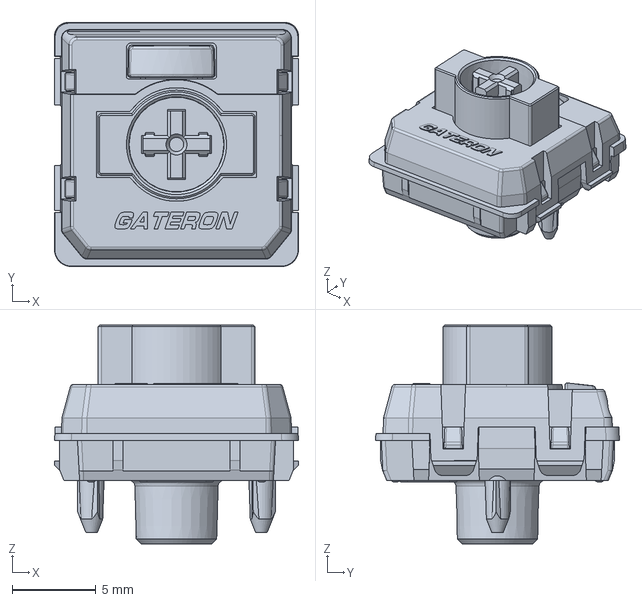
[picture p54: CAD file, 2025-10-28]
hardware/models/KS-33D-FB.step
14.6 x 14.6 x 13.1 mm
