Reverier-Xu/KeysDock/hardware/models/WQFN-16_L3.0-W3.0-P0.50-TL-EP1.7.step

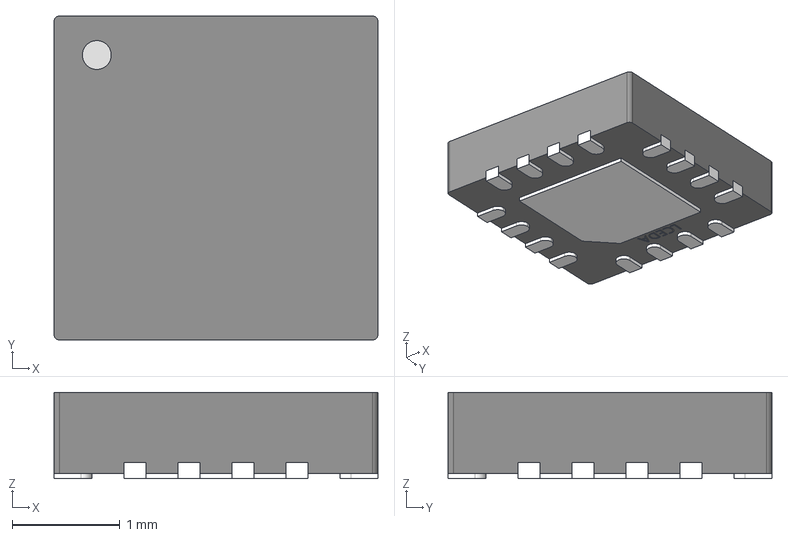
[picture p55: CAD file, 2025-10-28]
hardware/models/WQFN-16_L3.0-W3.0-P0.50-TL-EP1.7.step
3.00 x 3.00 x 0.8 mm
WQFN-16_L3.0-W3.0-P0.50-TL-EP1.7~WQFN-16_L3.0-W3.0-P0.50-TL-EP1.7~pSXh
WQFN-16_L3.0-W3.0-P0.50-TL-EP1.7~WQFN-16_ L3.0-W3.0-P0.50-TL-EP1.7~pSXh001
WQFN-16_L3.0-W3.0-P0.50-TL-EP1.7~WQFN-16_ L3.0-W3.0-P0.50-TL-EP1.7~pSXh002
WQFN-16_L3.0-W3.0-P0.50-TL-EP1.7~WQFN-16_ L3.0-W3.0-P0.50-TL-EP1.7~pSXh003
WQFN-16_L3.0-W3.0-P0.50-TL-EP1.7~WQFN-16_ L3.0-W3.0-P0.50-TL-EP1.7~pSXh004
WQFN-16_L3.0-W3.0-P0.50-TL-EP1.7~WQFN-16_ L3.0-W3.0-P0.50-TL-EP1.7~pSXh005
WQFN-16_L3.0-W3.0-P0.50-TL-EP1.7~WQFN-16_ L3.0-W3.0-P0.50-TL-EP1.7~pSXh006
WQFN-16_L3.0-W3.0-P0.50-TL-EP1.7~WQFN-16_ L3.0-W3.0-P0.50-TL-EP1.7~pSXh007
WQFN-16_L3.0-W3.0-P0.50-TL-EP1.7~WQFN-16_ L3.0-W3.0-P0.50-TL-EP1.7~pSXh008
WQFN-16_L3.0-W3.0-P0.50-TL-EP1.7~WQFN-16_ L3.0-W3.0-P0.50-TL-EP1.7~pSXh009
WQFN-16_L3.0-W3.0-P0.50-TL-EP1.7~WQFN-16_ L3.0-W3.0-P0.50-TL-EP1.7~pSXh010
WQFN-16_L3.0-W3.0-P0.50-TL-EP1.7~WQFN-16_ L3.0-W3.0-P0.50-TL-EP1.7~pSXh011
WQFN-16_L3.0-W3.0-P0.50-TL-EP1.7~WQFN-16_ L3.0-W3.0-P0.50-TL-EP1.7~pSXh012
WQFN-16_L3.0-W3.0-P0.50-TL-EP1.7~WQFN-16_ L3.0-W3.0-P0.50-TL-EP1.7~pSXh013
WQFN-16_L3.0-W3.0-P0.50-TL-EP1.7~WQFN-16_ L3.0-W3.0-P0.50-TL-EP1.7~pSXh014
WQFN-16_L3.0-W3.0-P0.50-TL-EP1.7~WQFN-16_ L3.0-W3.0-P0.50-TL-EP1.7~pSXh015
WQFN-16_L3.0-W3.0-P0.50-TL-EP1.7~WQFN-16_ L3.0-W3.0-P0.50-TL-EP1.7~pSXh016
WQFN-16_L3.0-W3.0-P0.50-TL-EP1.7~WQFN-16_ L3.0-W3.0-P0.50-TL-EP1.7~pSXh017
