Reverier-Xu/KeysDock/hardware/models/R_0603.step

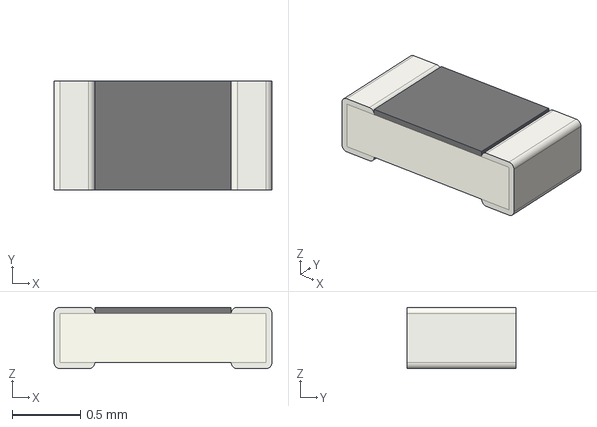
[picture p56: CAD file, 2025-10-28]
hardware/models/R_0603.step
1.60 x 0.8 x 0.45 mm
