Reverier-Xu/KeysDock/suitekits/PackBox.pdf

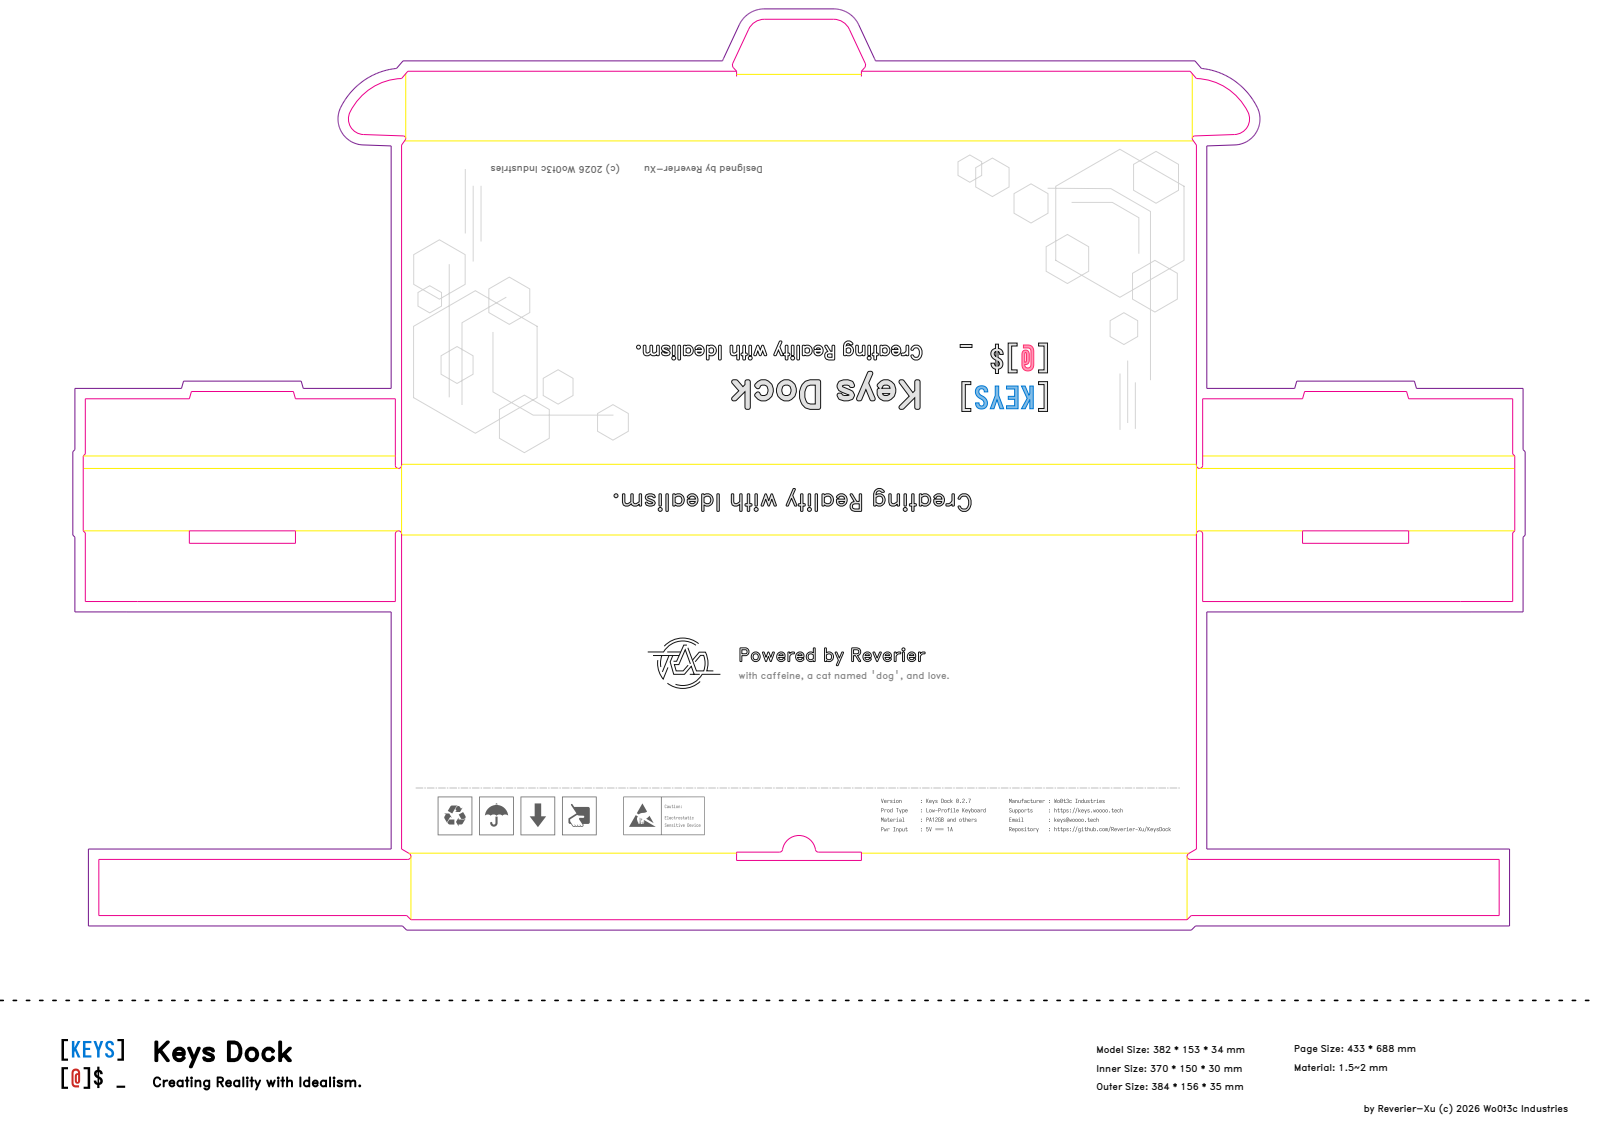
[picture p112: page 1]

with caffeine, a cat named 'dog', and love.

Model Size: 382 * 153 * 34 mm
Inner Size: 370 * 150 * 30 mm
Outer Size: 384 * 156 * 35 mm

Page Size: 433 * 688 mm
Material: 1.5~2 mm

by Reverier-Xu (c) 2026 Wo0t3c Industries
